iikolodziej/Digital-analog-panel-meter-clock-on-AVR/images/pcb bottom psc.png

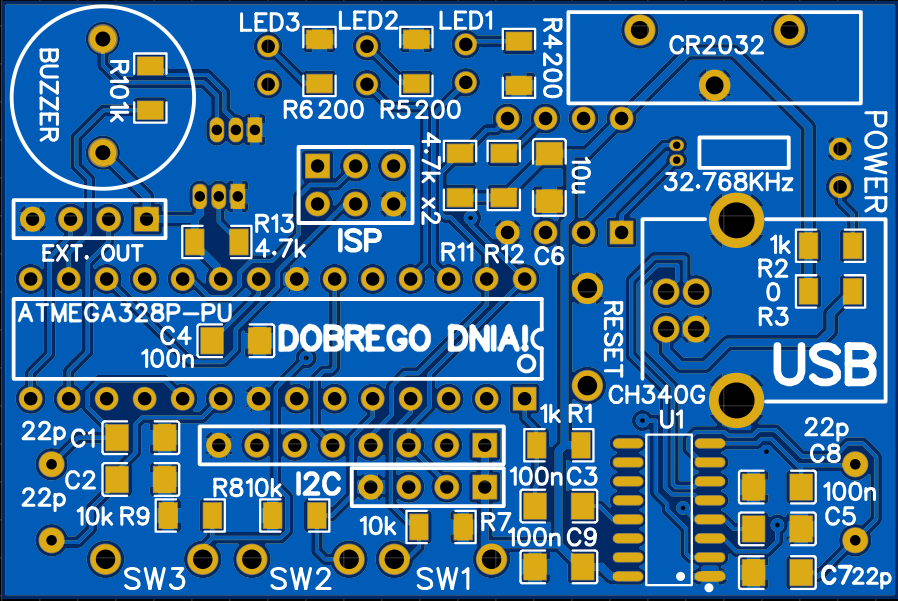
images/pcb bottom psc.png
